b-s-code/thumbdox/docs/design/images/exploded_render_joins_and_cutouts.png

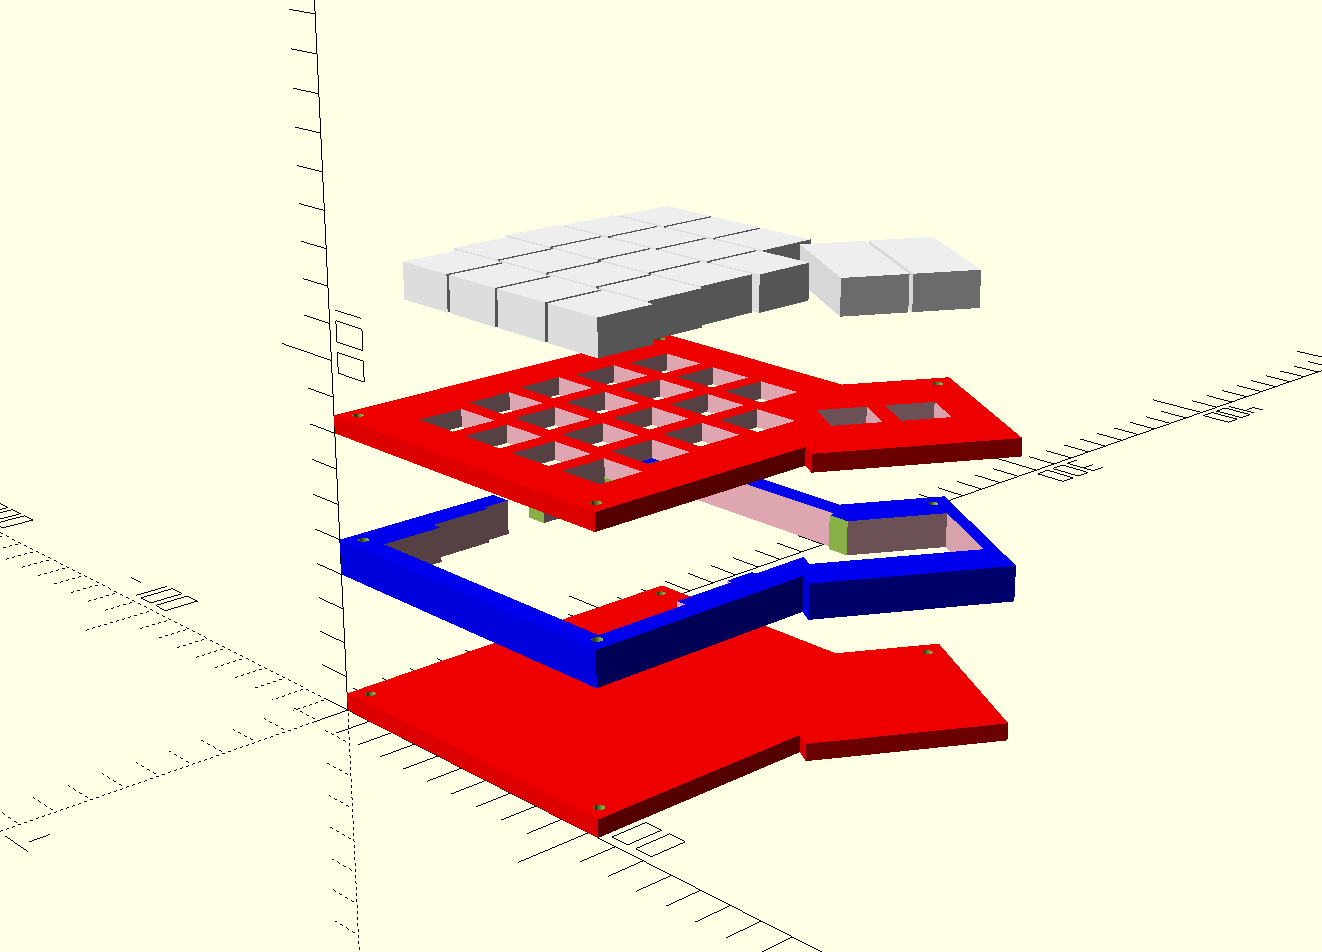
docs/design/images/exploded_render_joins_and_cutouts.png
