b-s-code/thumbdox/docs/design/images/key_positions_tuned_underside.png

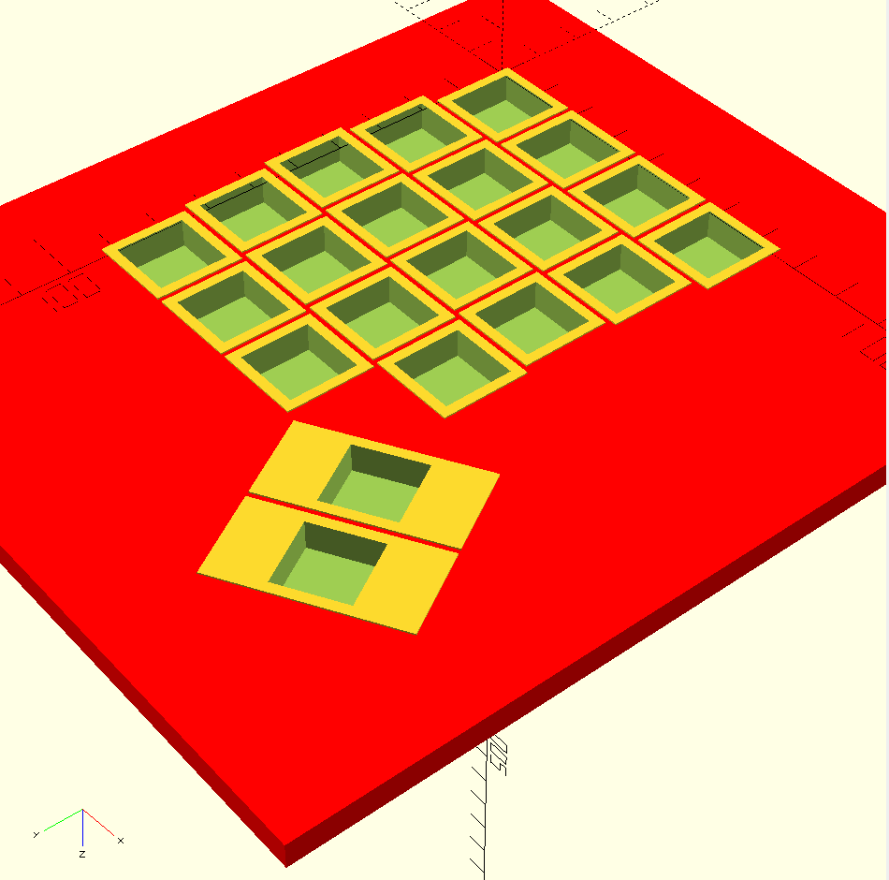
docs/design/images/key_positions_tuned_underside.png
