b-s-code/thumbdox/docs/design/images/LHS_and_exploded_view.png

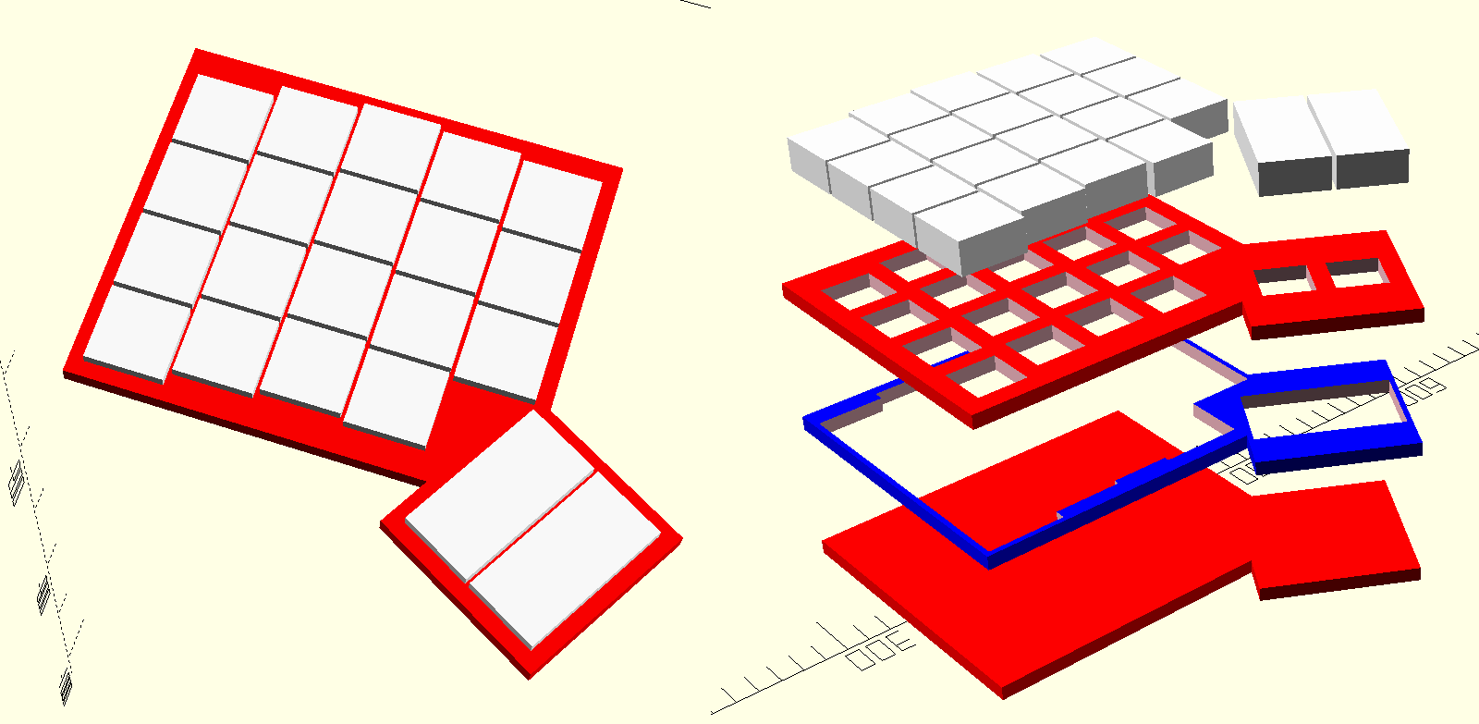
docs/design/images/LHS_and_exploded_view.png
