b-s-code/thumbdox/docs/design/images/MCU_TRRS_slots_positioned.png

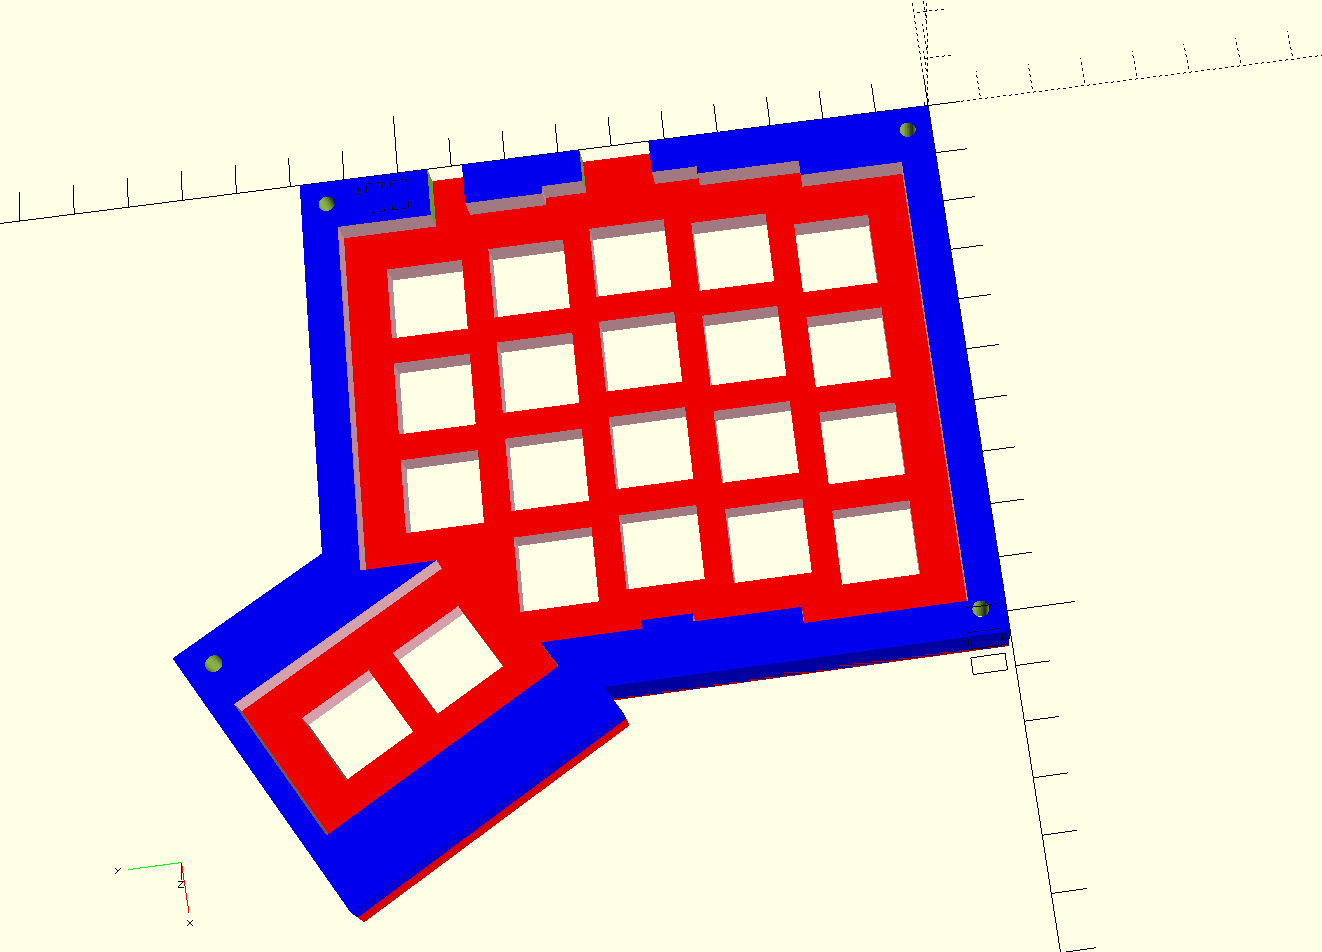
docs/design/images/MCU_TRRS_slots_positioned.png
