b-s-code/thumbdox/docs/design/images/thumbdox_LHS.png

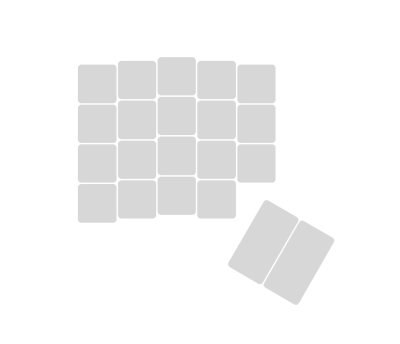
docs/design/images/thumbdox_LHS.png
