b-s-code/thumbdox/docs/design/images/thumbdox_LHS_early_concept.png

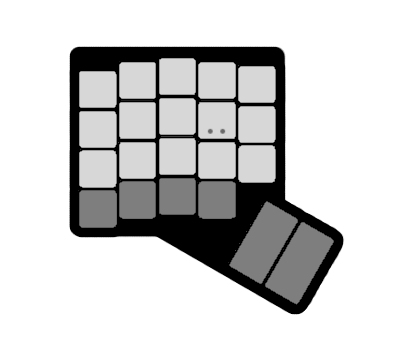
docs/design/images/thumbdox_LHS_early_concept.png
