b-s-code/thumbdox/docs/design/images/transparent_keycaps.png

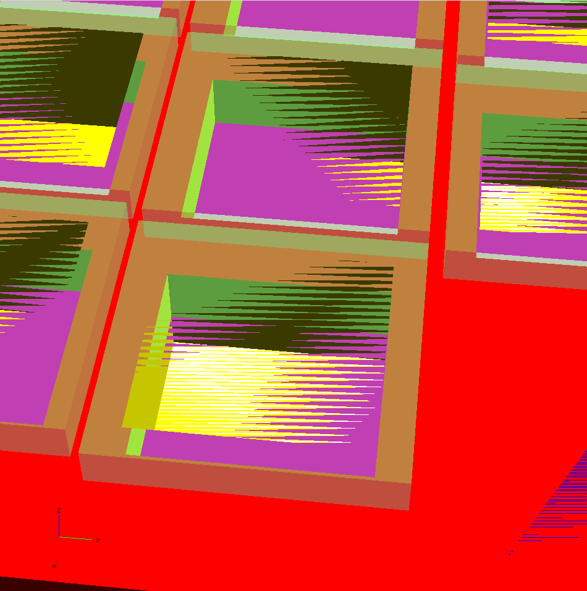
docs/design/images/transparent_keycaps.png
