b-s-code/thumbdox/docs/design/images/z-fighting.png

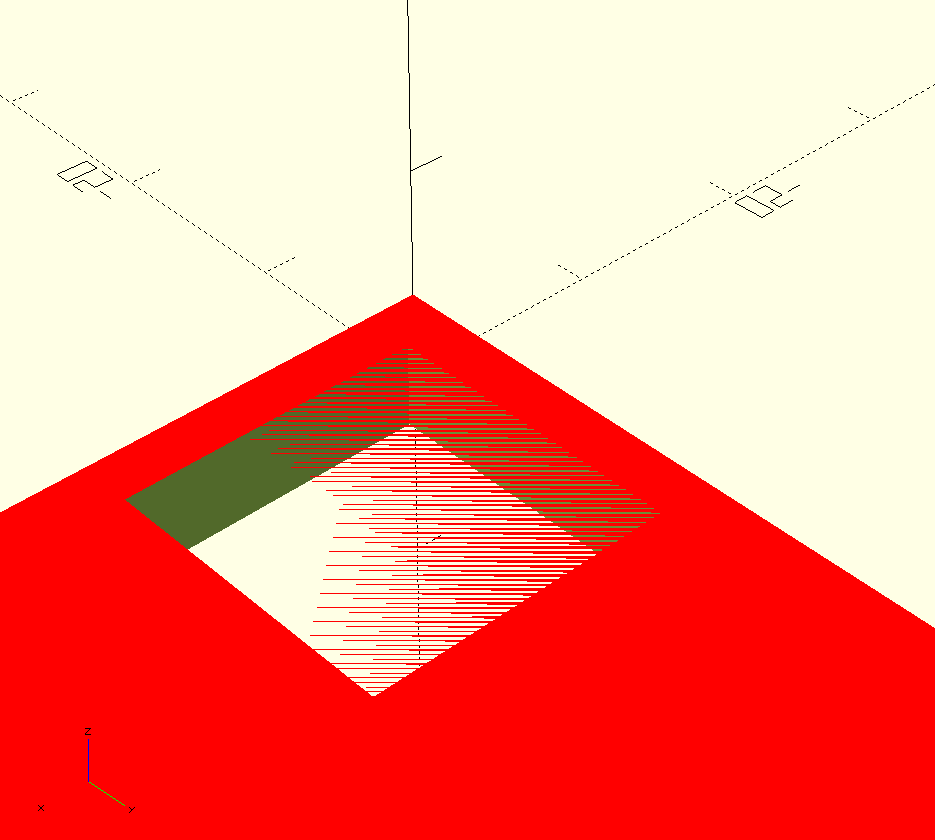
docs/design/images/z-fighting.png
