b-s-code/thumbdox/docs/design/images/z-fighting_resolved.png

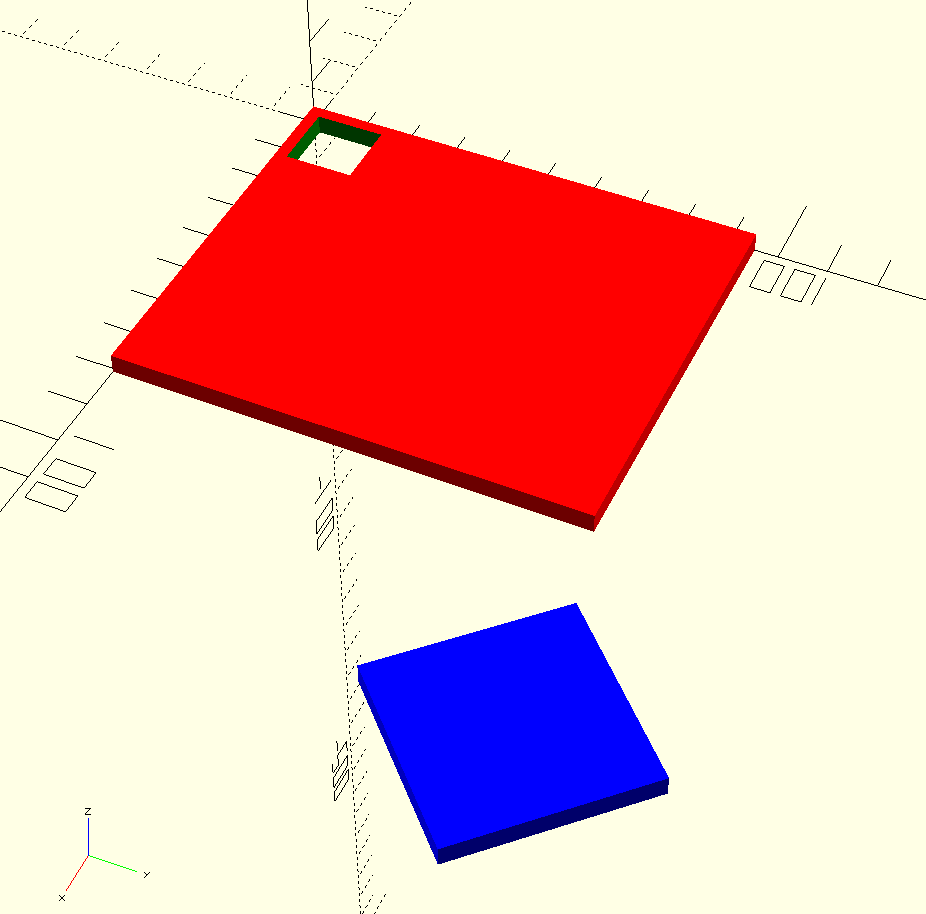
docs/design/images/z-fighting_resolved.png
