b-s-code/thumbdox/docs/design/images/concatenated_parts_DXF_1.png

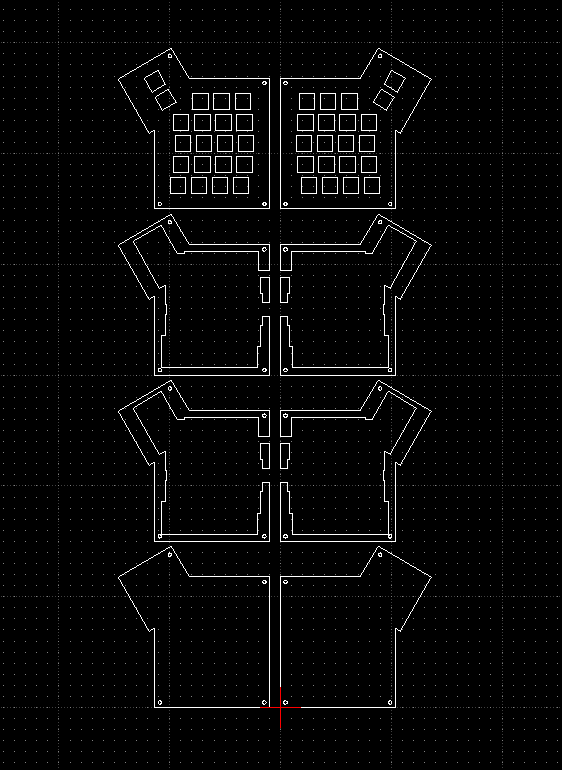
docs/design/images/concatenated_parts_DXF_1.png
