b-s-code/thumbdox/docs/design/images/concatenated_parts_preview.png

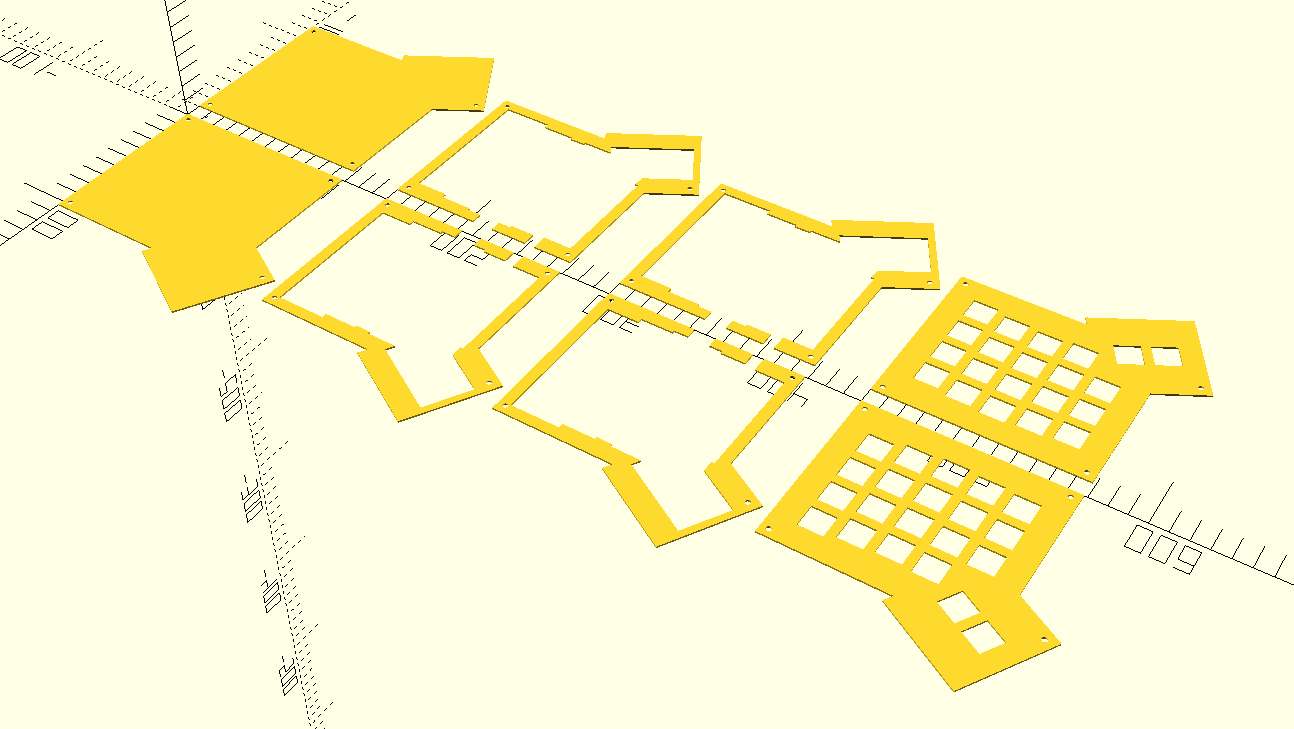
docs/design/images/concatenated_parts_preview.png
