b-s-code/thumbdox/docs/design/images/flush_parts2.png

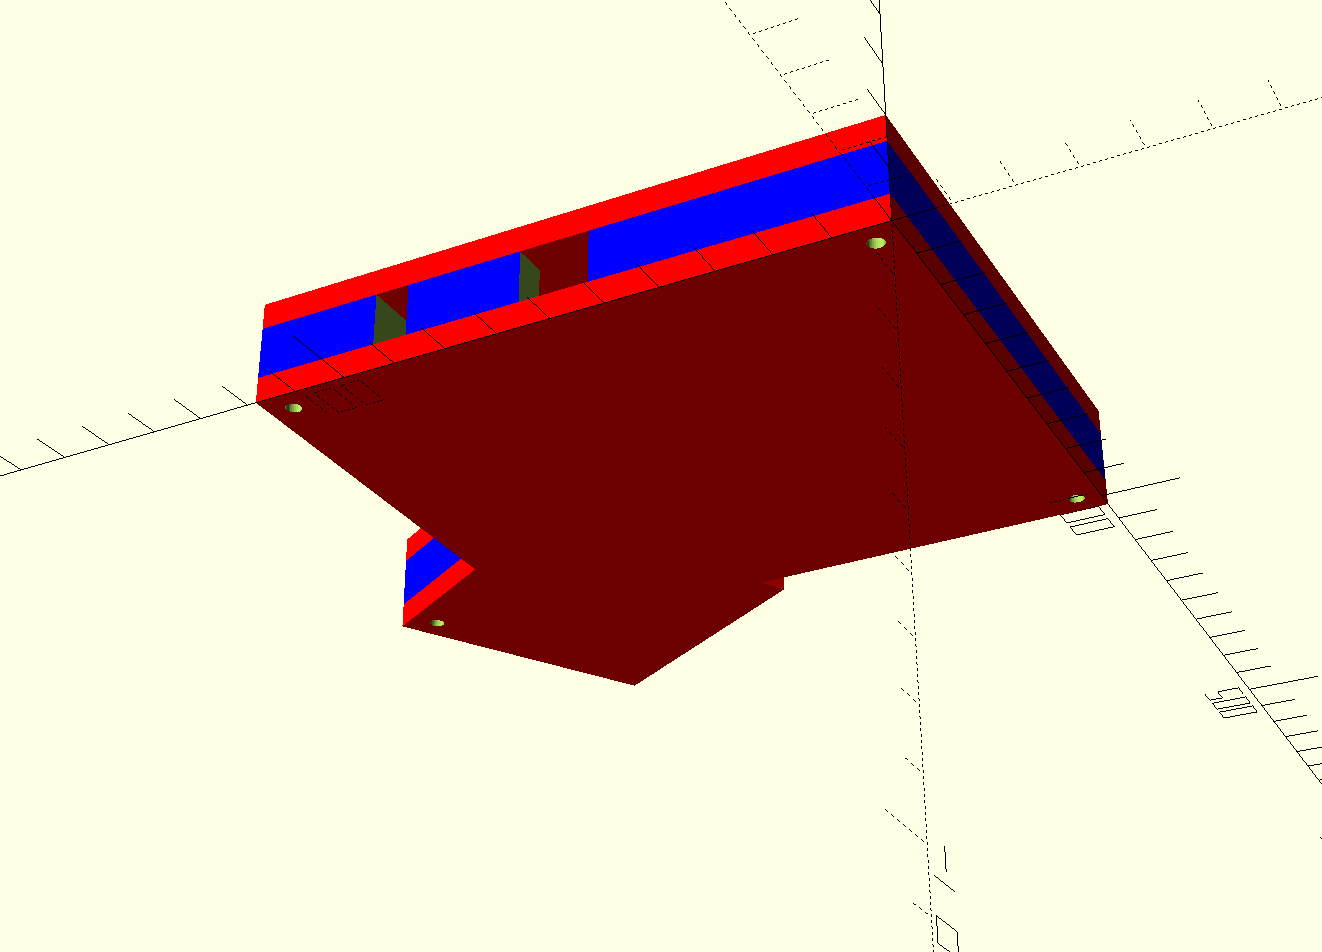
docs/design/images/flush_parts2.png
