b-s-code/thumbdox/docs/design/images/flush_parts.png

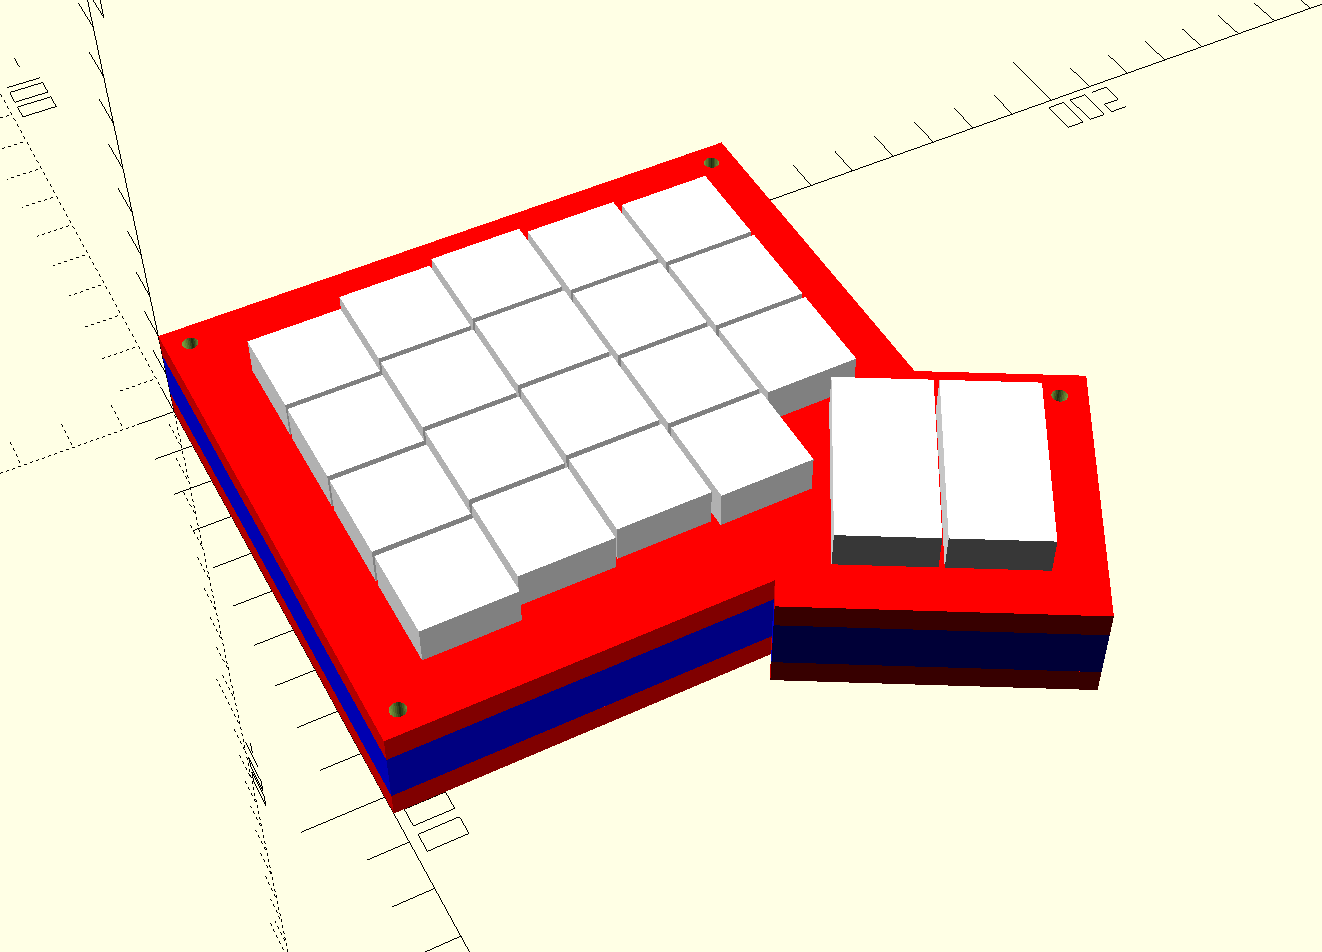
docs/design/images/flush_parts.png
