b-s-code/thumbdox/docs/assembly/assembly_process.png

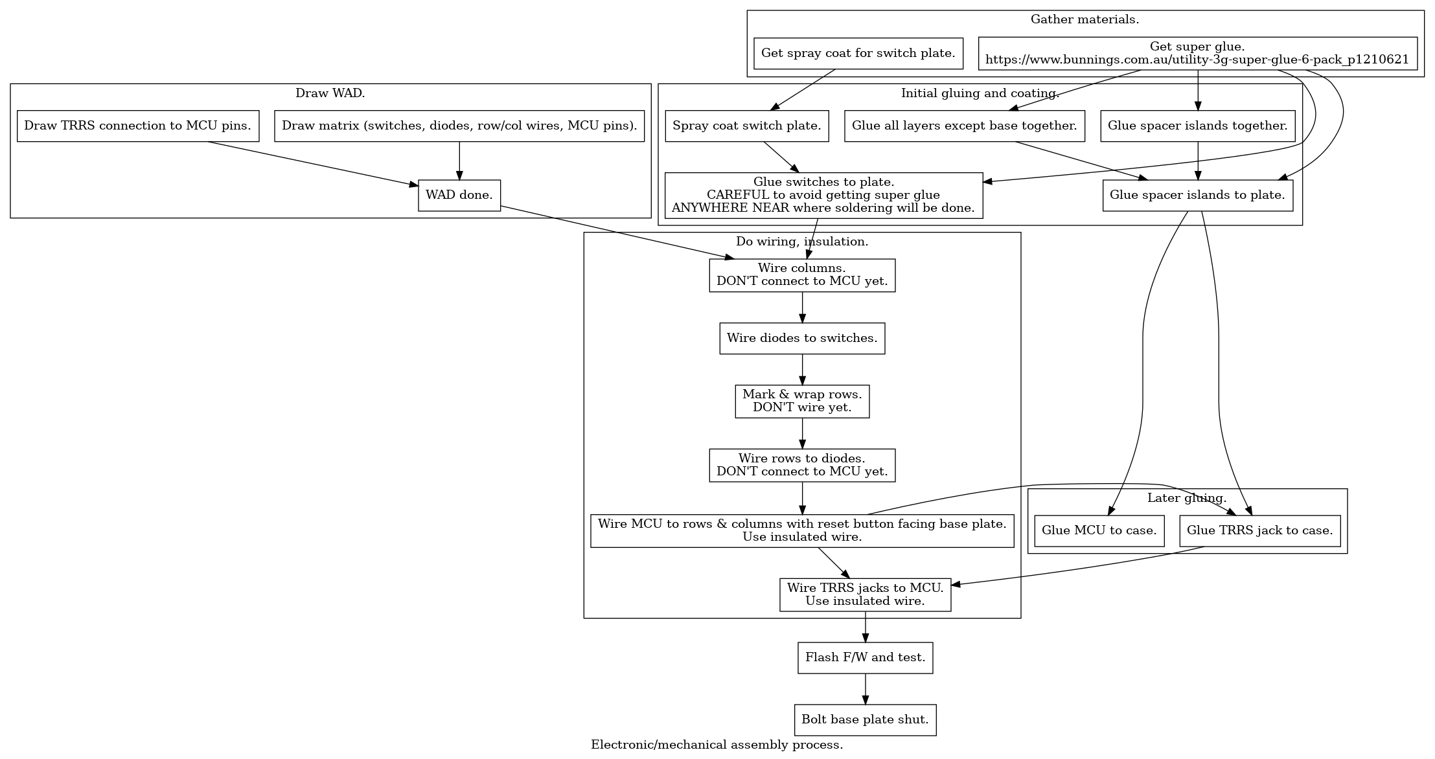
docs/assembly/assembly_process.png
