b-s-code/thumbdox/docs/assembly/img/both_sides_no_thumb_switches.jpg

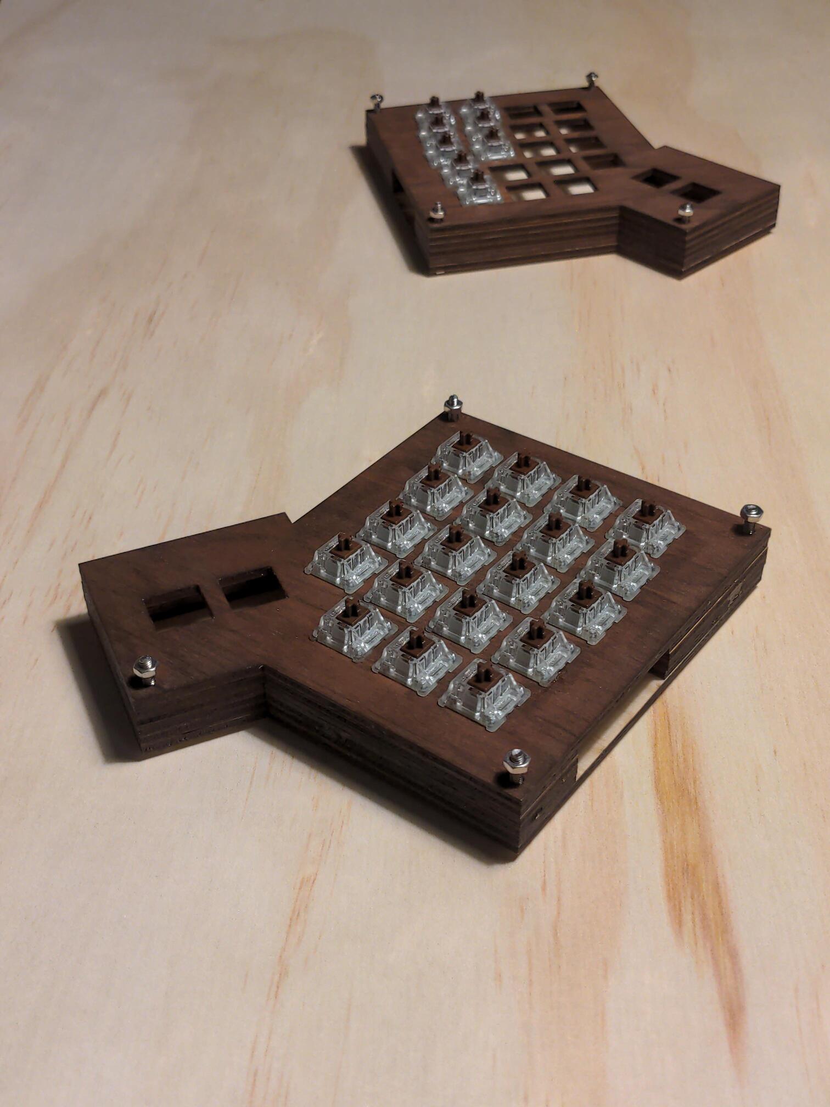
docs/assembly/img/both_sides_no_thumb_switches.jpg
