b-s-code/thumbdox/docs/assembly/img/lhs_finger_switches.jpg

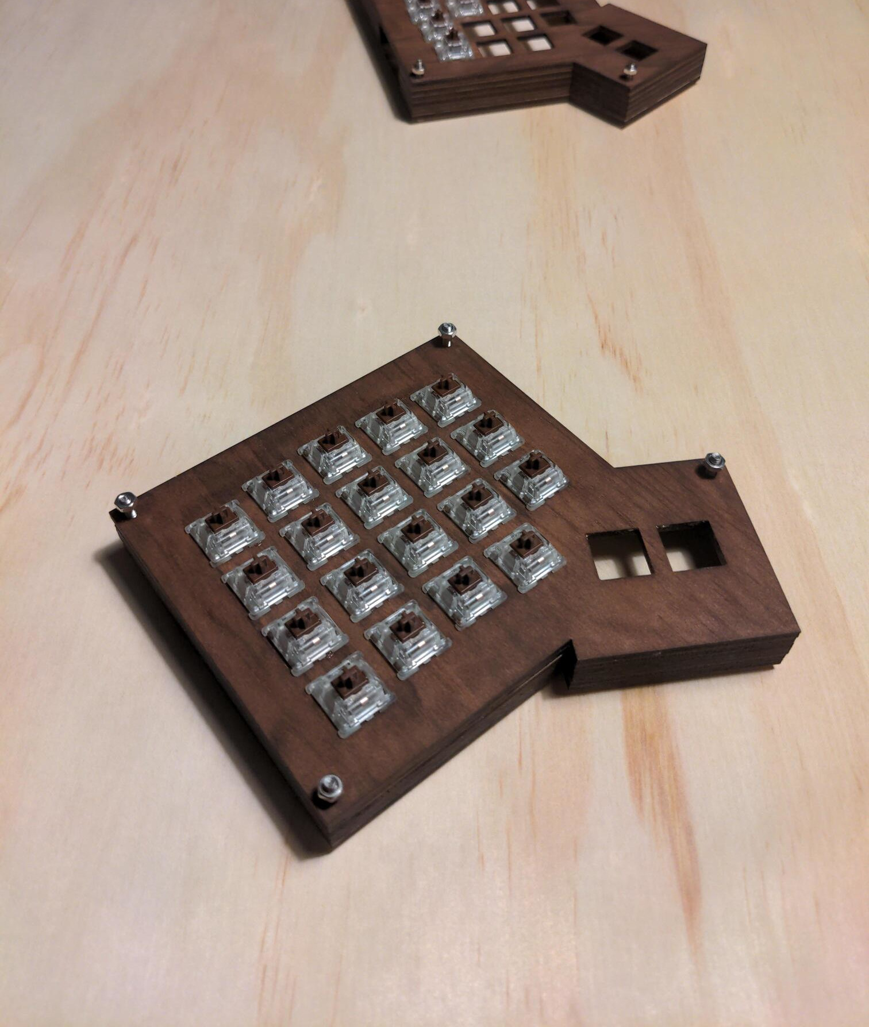
docs/assembly/img/lhs_finger_switches.jpg
