b-s-code/thumbdox/docs/assembly/img/mcu_trrs_void.jpg

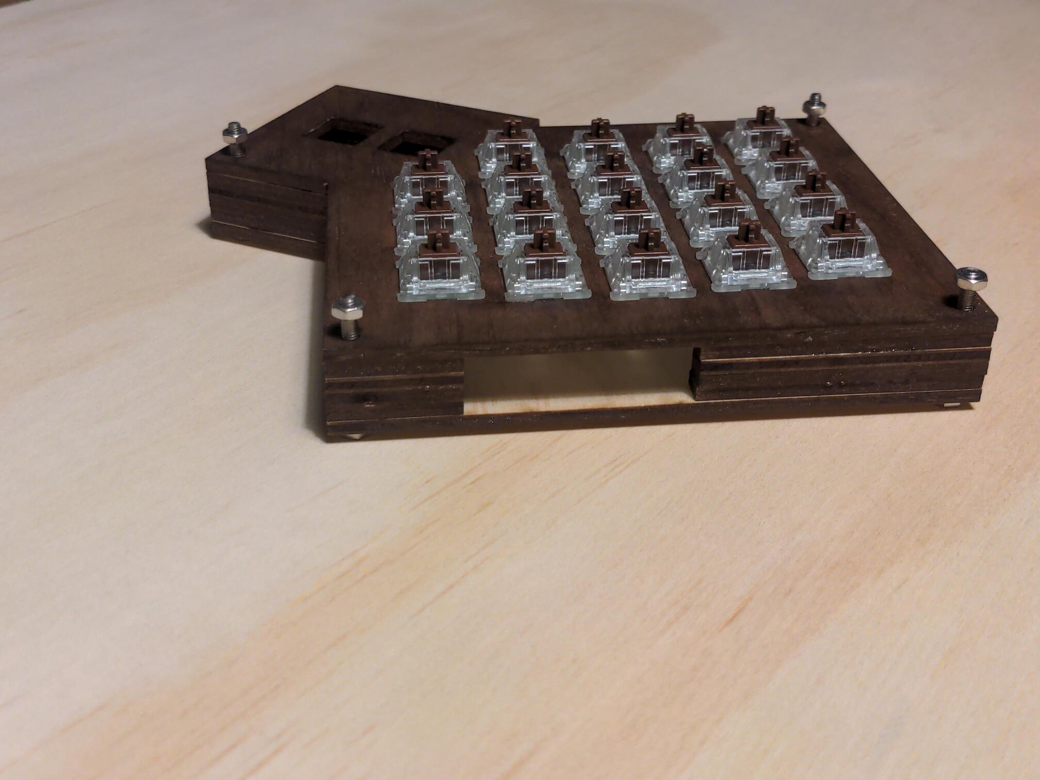
docs/assembly/img/mcu_trrs_void.jpg
