b-s-code/thumbdox/docs/assembly/img/plate_switches.jpg

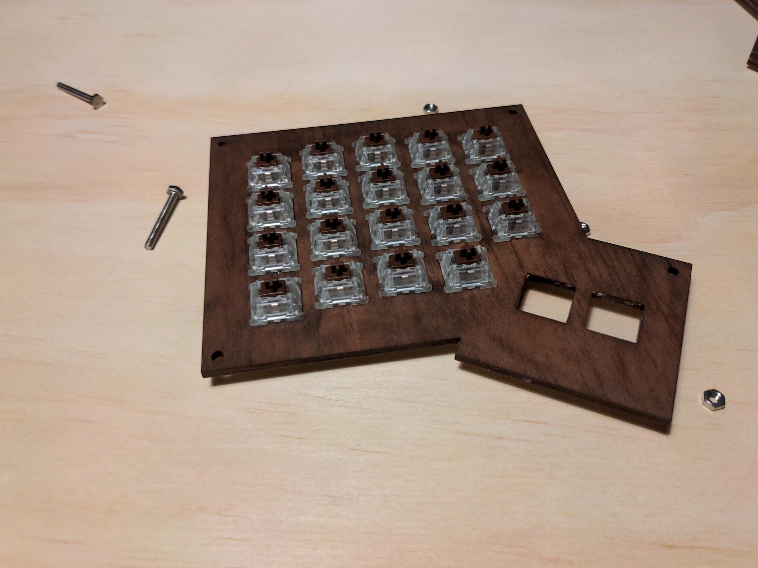
docs/assembly/img/plate_switches.jpg
