b-s-code/thumbdox/docs/assembly/img/rhs_some_switches.jpg

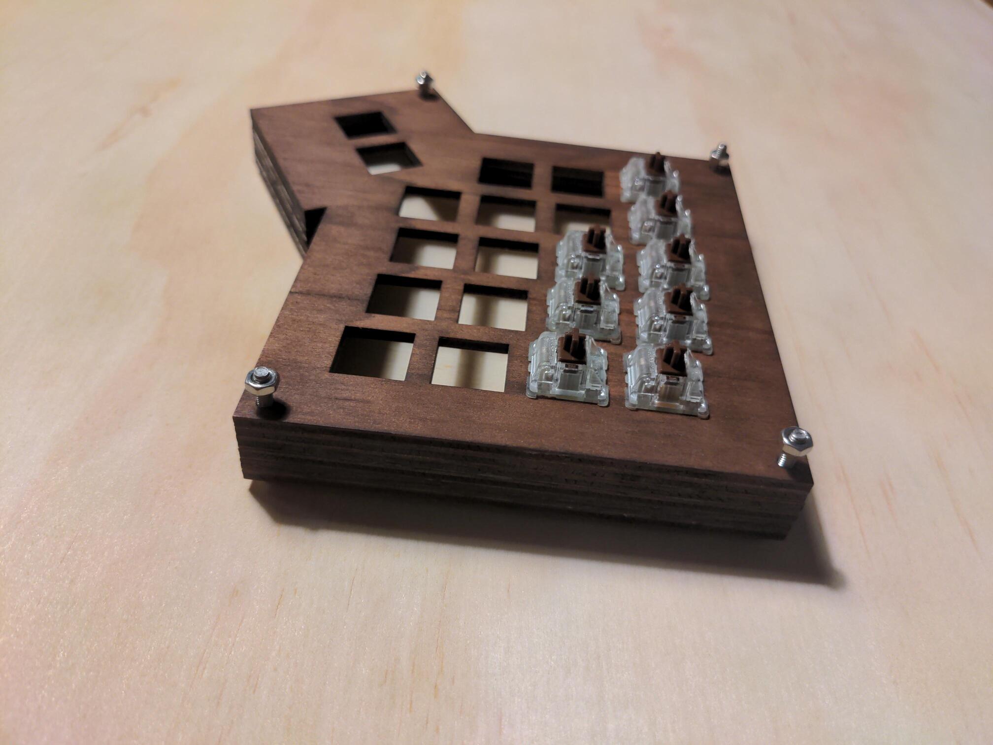
docs/assembly/img/rhs_some_switches.jpg
