b-s-code/thumbdox/docs/assembly/img/spacer_layers.jpg

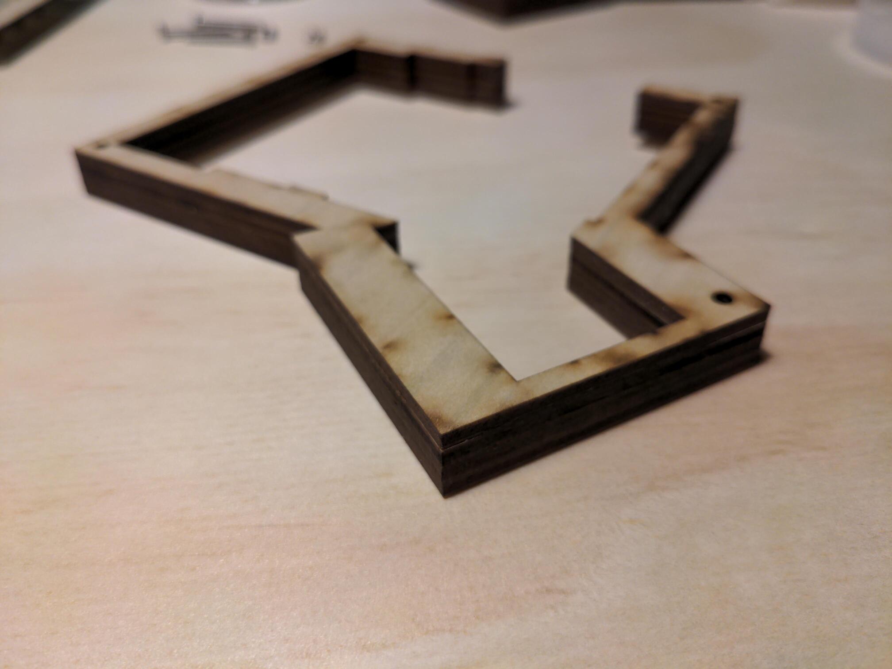
docs/assembly/img/spacer_layers.jpg
