b-s-code/thumbdox/docs/assembly/img/underside_not_wired.jpg

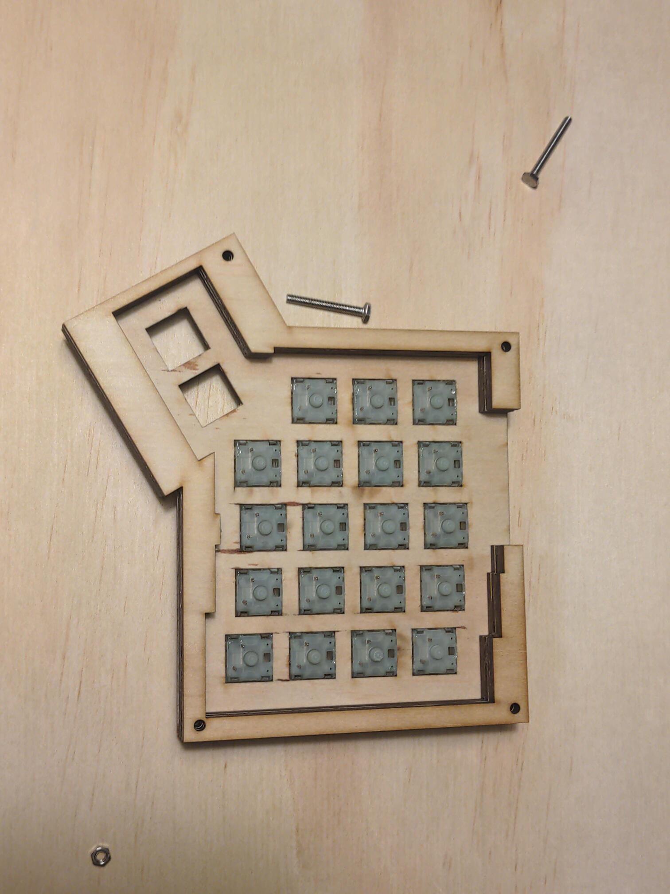
docs/assembly/img/underside_not_wired.jpg
