b-s-code/thumbdox/docs/assembly/img/WAD/dual_trrs_unzoomed.jpg

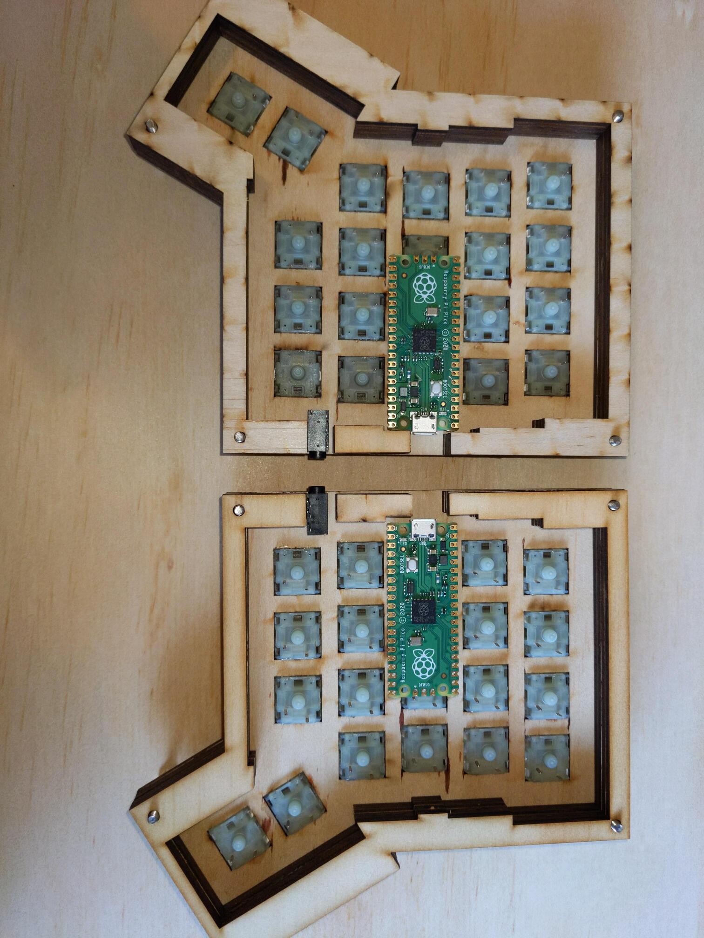
docs/assembly/img/WAD/dual_trrs_unzoomed.jpg
