b-s-code/thumbdox/docs/assembly/img/WAD/dual_ttrs.jpg

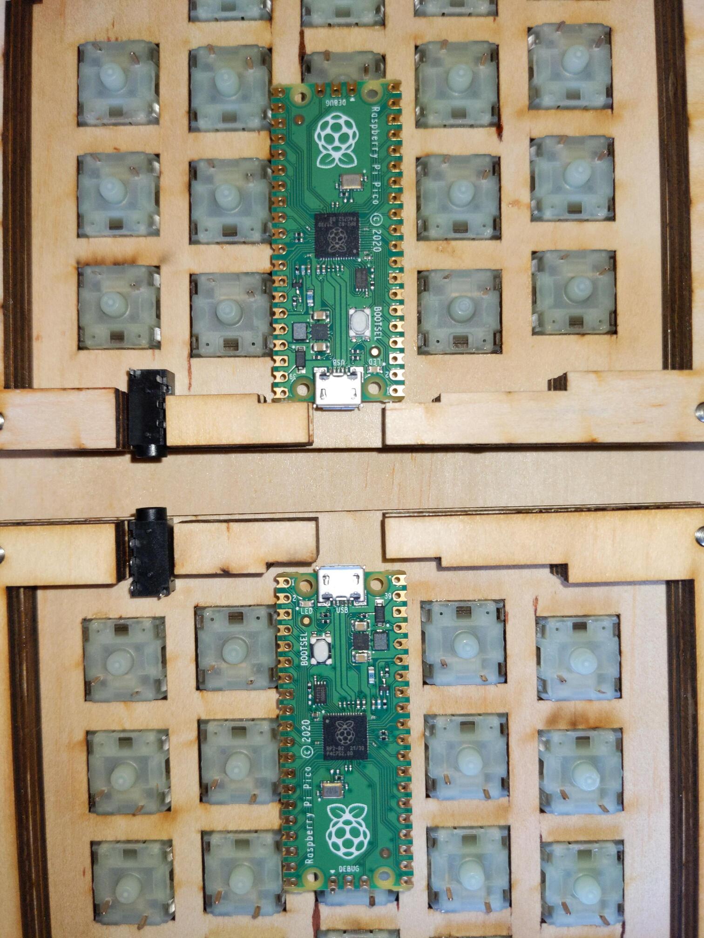
docs/assembly/img/WAD/dual_ttrs.jpg
