b-s-code/thumbdox/docs/assembly/img/WAD/dual_ttrs.png

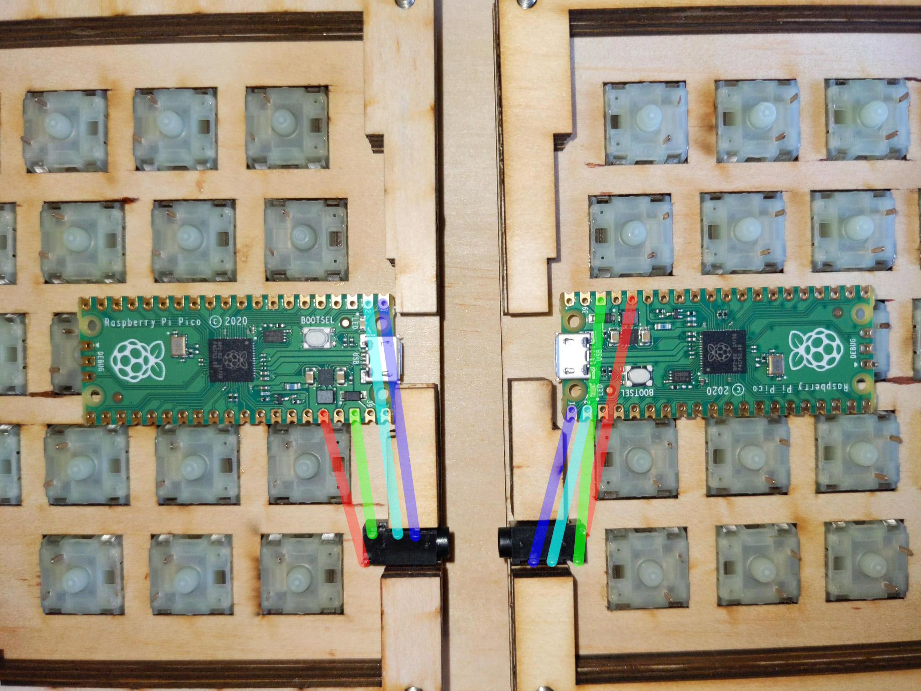
docs/assembly/img/WAD/dual_ttrs.png
