b-s-code/thumbdox/docs/assembly/img/WAD/mcu_front.jpg

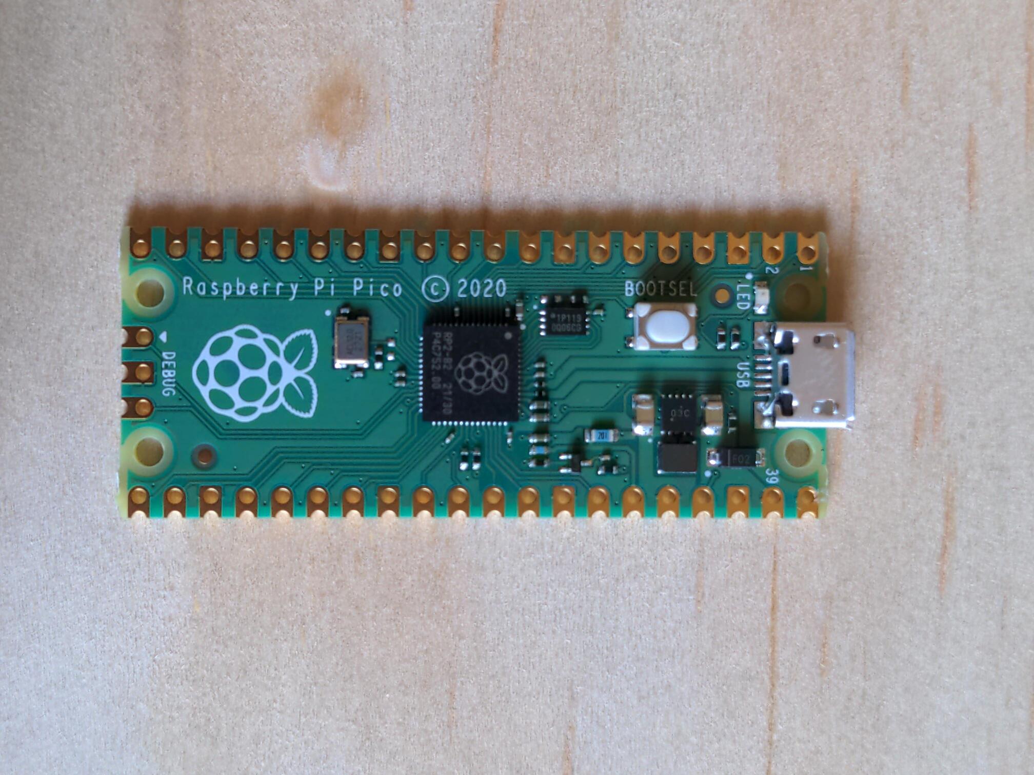
docs/assembly/img/WAD/mcu_front.jpg
