b-s-code/thumbdox/docs/assembly/img/WAD/mcu_front_and_back.jpg

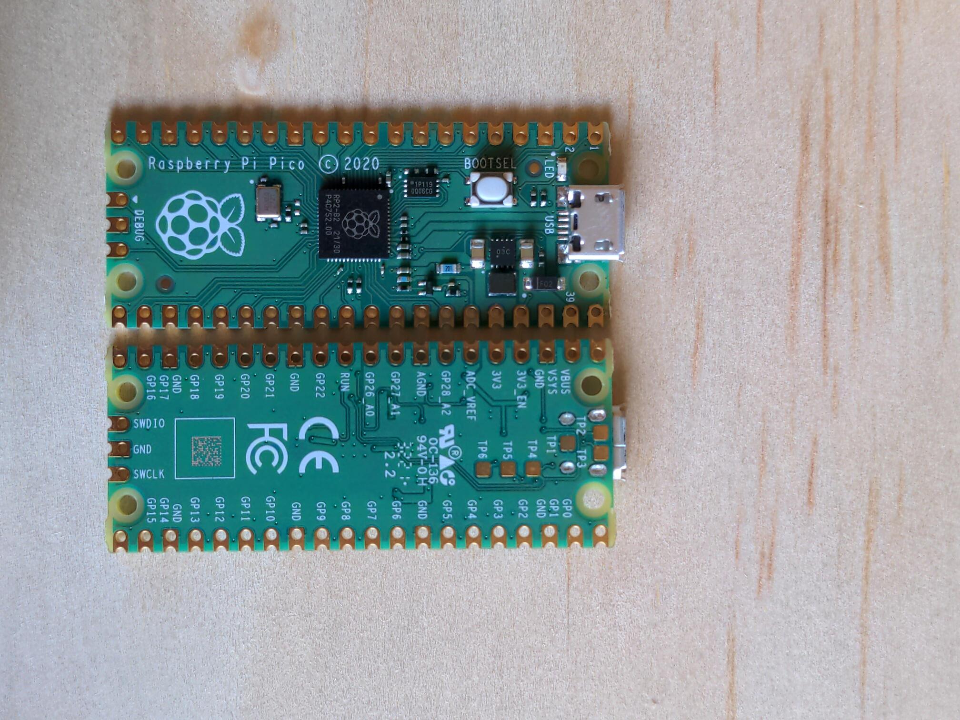
docs/assembly/img/WAD/mcu_front_and_back.jpg
