b-s-code/thumbdox/docs/assembly/img/WAD/mcus_lhs_rhs_flat_lay.jpg

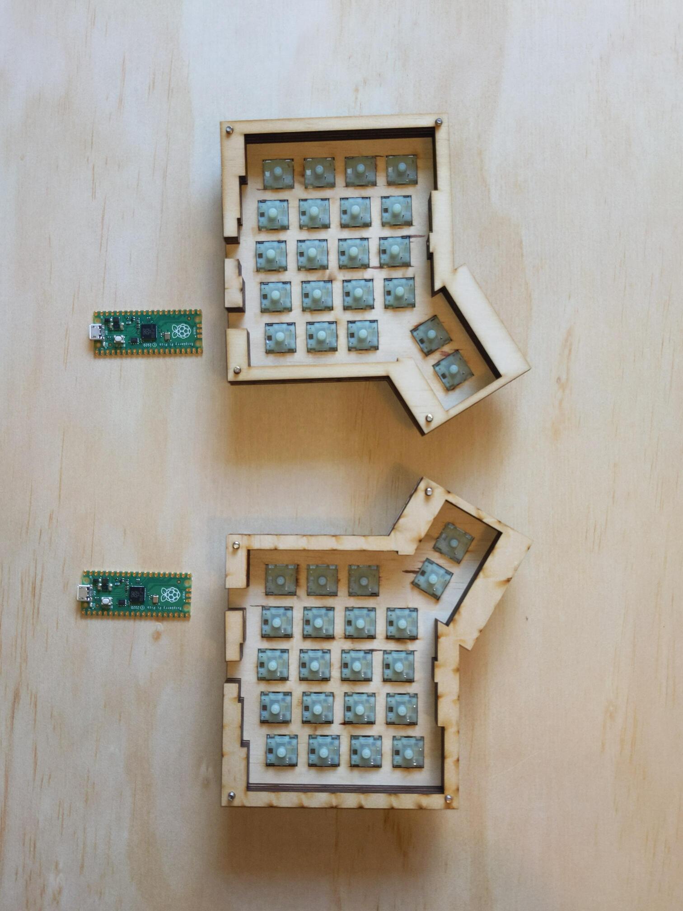
docs/assembly/img/WAD/mcus_lhs_rhs_flat_lay.jpg
