b-s-code/thumbdox/docs/assembly/img/WAD/mcus_overlaid.jpg

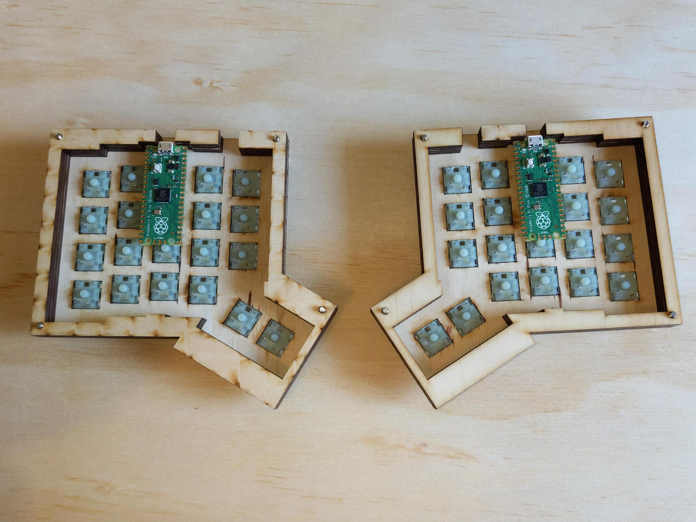
docs/assembly/img/WAD/mcus_overlaid.jpg
