b-s-code/thumbdox/docs/assembly/img/WAD/mcus_overlaid_2.jpg

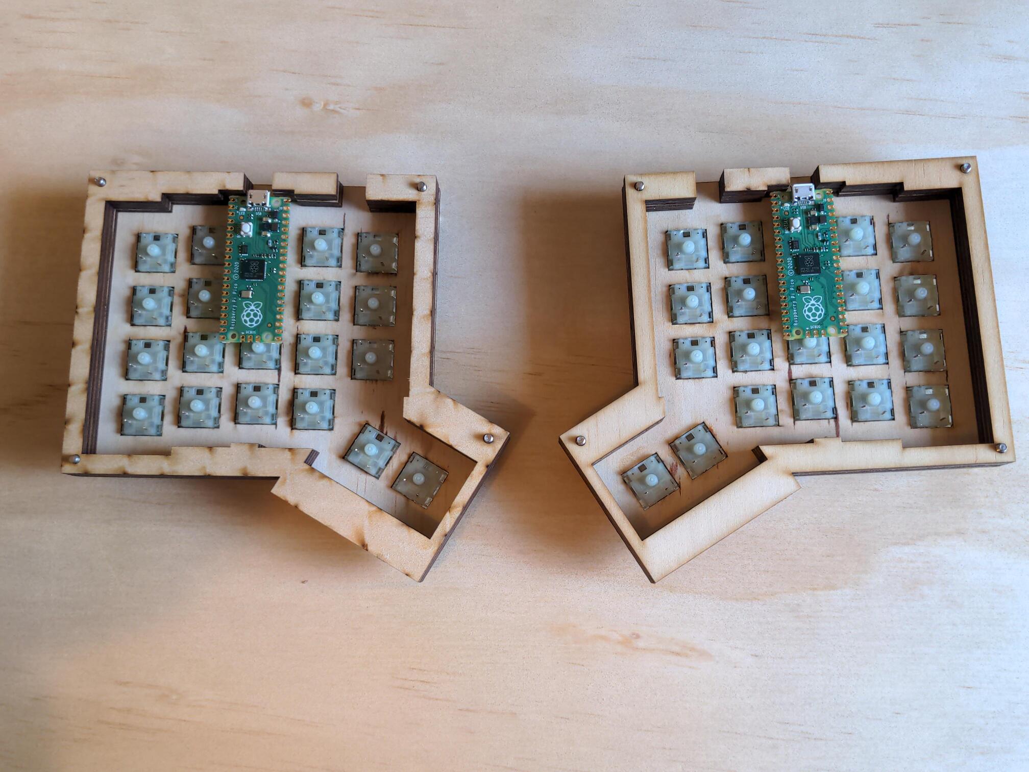
docs/assembly/img/WAD/mcus_overlaid_2.jpg
