b-s-code/thumbdox/docs/assembly/img/WAD/mcus_trrs_overlaid.jpg

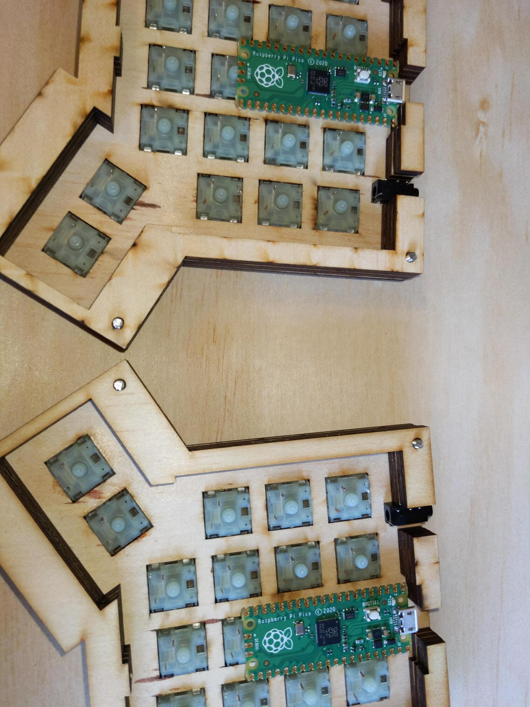
docs/assembly/img/WAD/mcus_trrs_overlaid.jpg
