b-s-code/thumbdox/docs/assembly/img/WAD/no_mcus.jpg

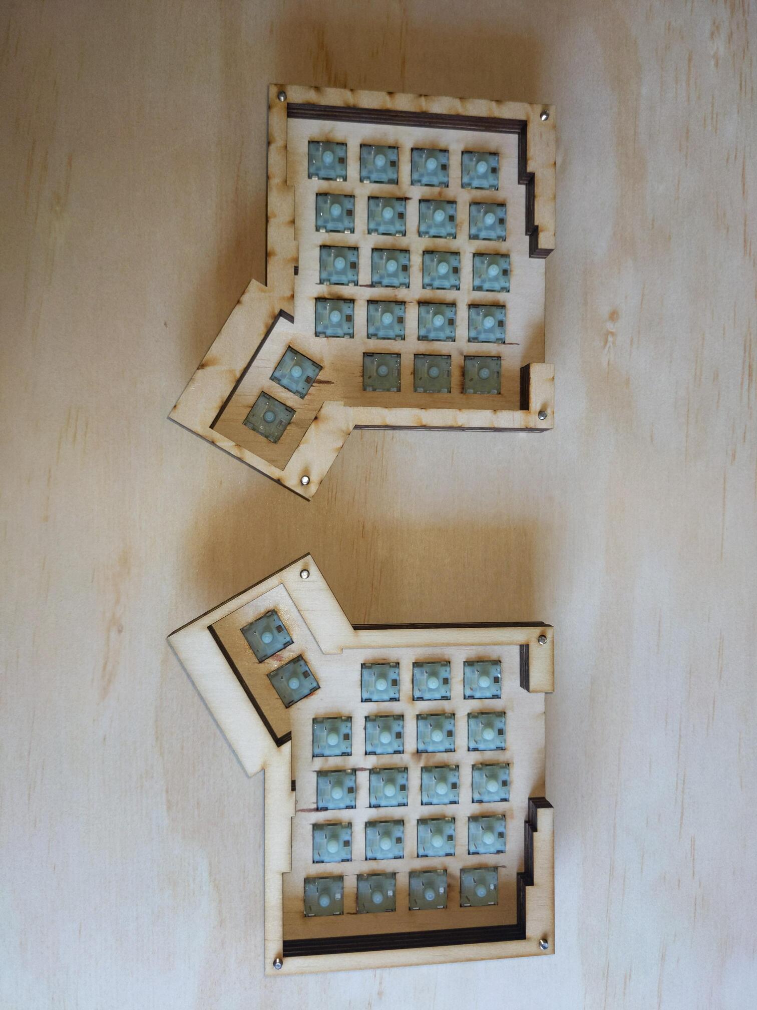
docs/assembly/img/WAD/no_mcus.jpg
