b-s-code/thumbdox/docs/assembly/img/WAD/overall_wiring.png

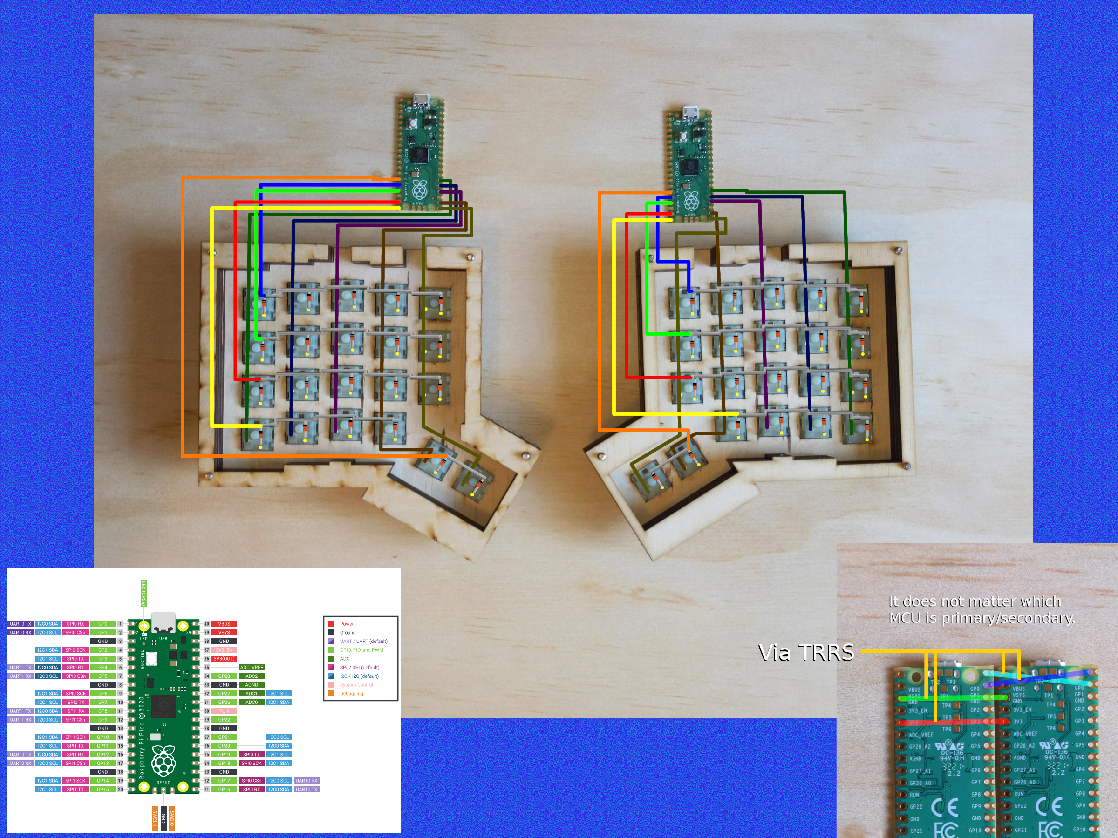
docs/assembly/img/WAD/overall_wiring.png
