b-s-code/thumbdox/docs/assembly/img/WAD/trrs_pins.png

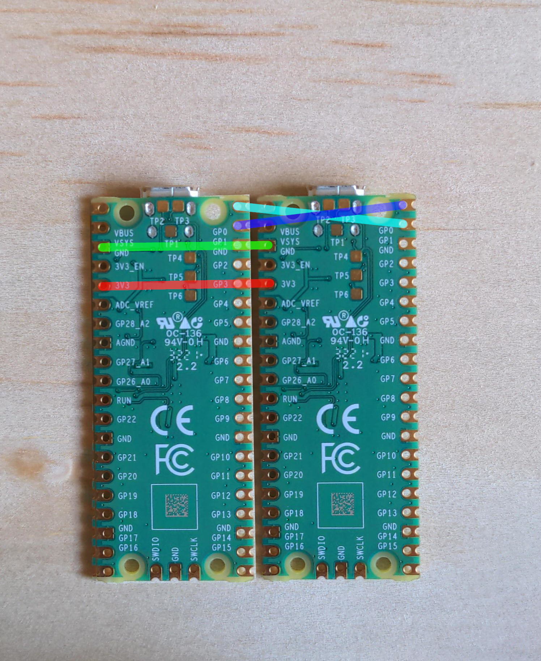
docs/assembly/img/WAD/trrs_pins.png
