b-s-code/thumbdox/docs/design/images/hacked_subtrahend_for_tuning_key_positions.png

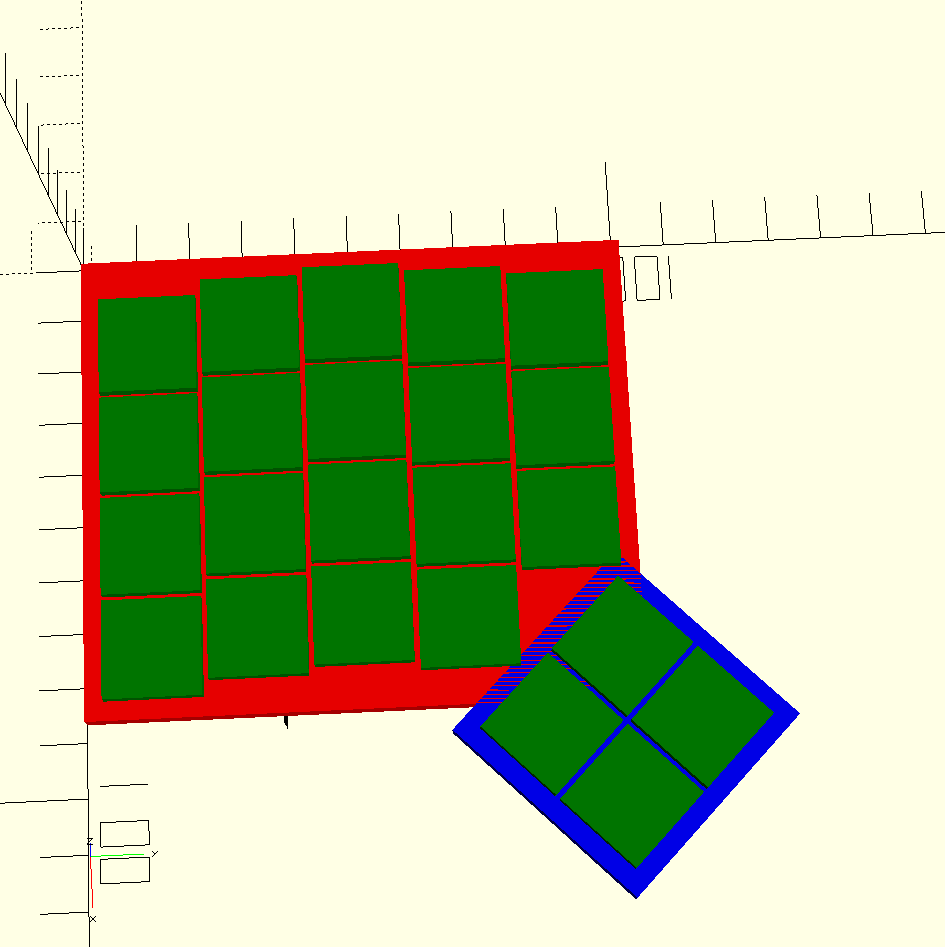
docs/design/images/hacked_subtrahend_for_tuning_key_positions.png
